Neoguitarist/captobox/resources/CAO carte électronique/fichiers sources/silk/capto.png

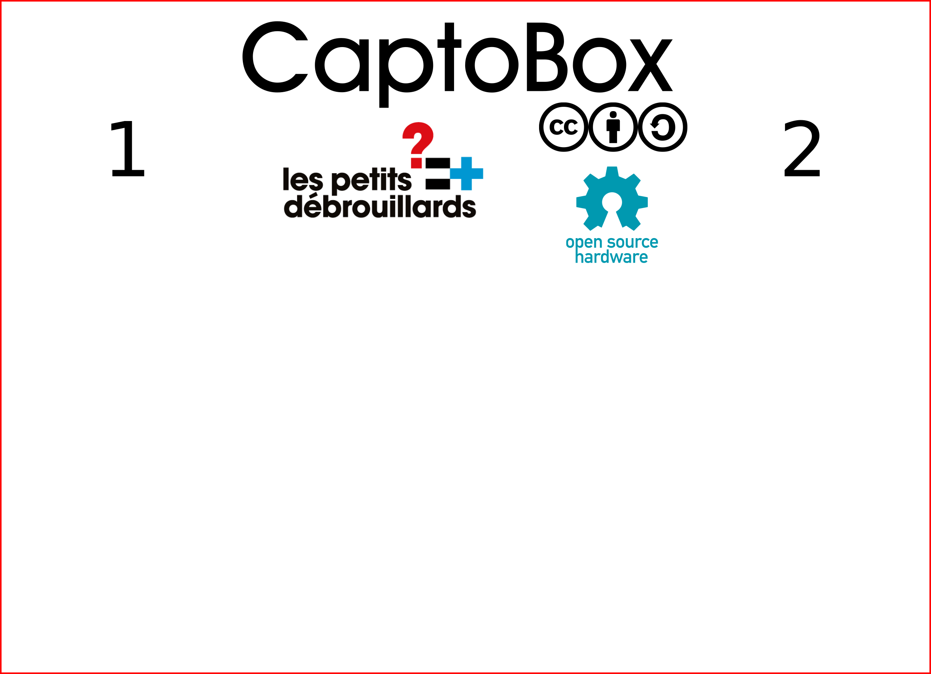
resources/CAO carte électronique/fichiers sources/silk/capto.png
