Neoguitarist/captobox/resources/CAO carte électronique/fichiers sources/silk/captobox-B_SilkS.png

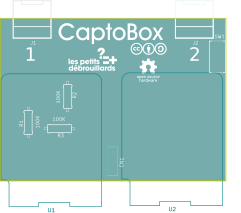
resources/CAO carte électronique/fichiers sources/silk/captobox-B_SilkS.png
