Neoguitarist/captobox/resources/CAO carte électronique/fichiers sources/silk/captobox-F_SilkS.png

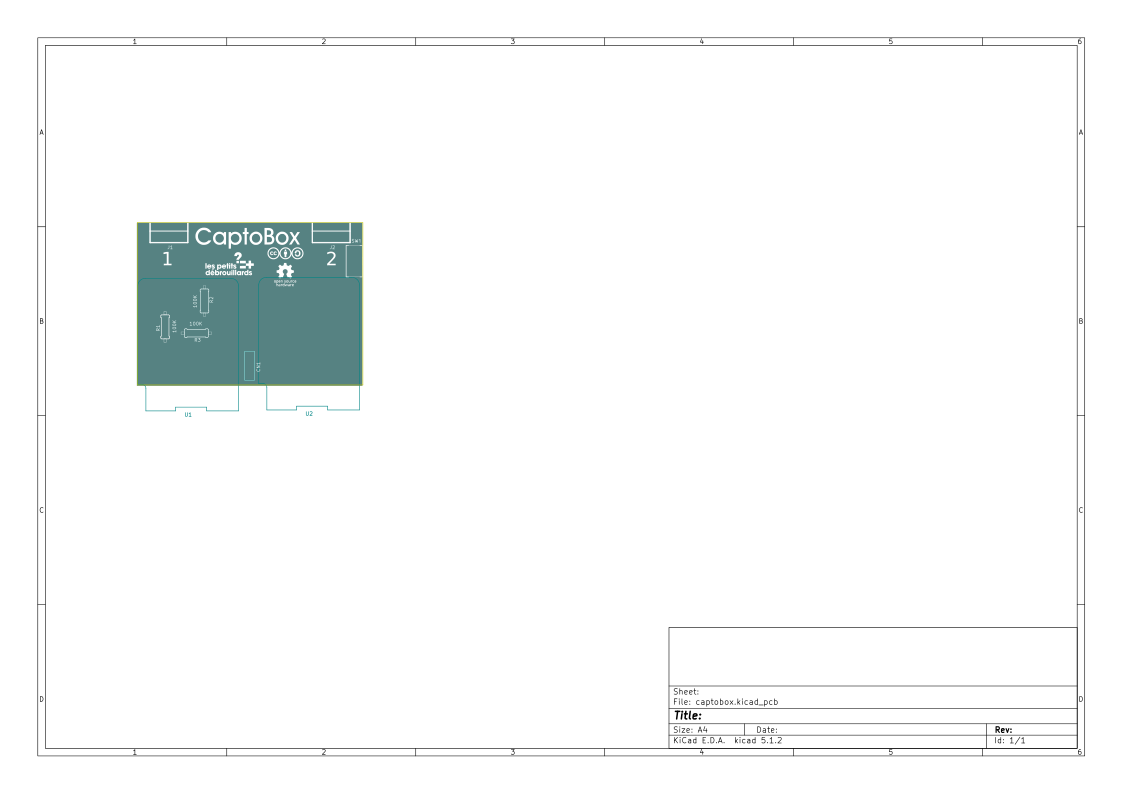
resources/CAO carte électronique/fichiers sources/silk/captobox-F_SilkS.png
