Neoguitarist/captobox/resources/CAO carte électronique/fichiers sources/silk/captobox-final.png

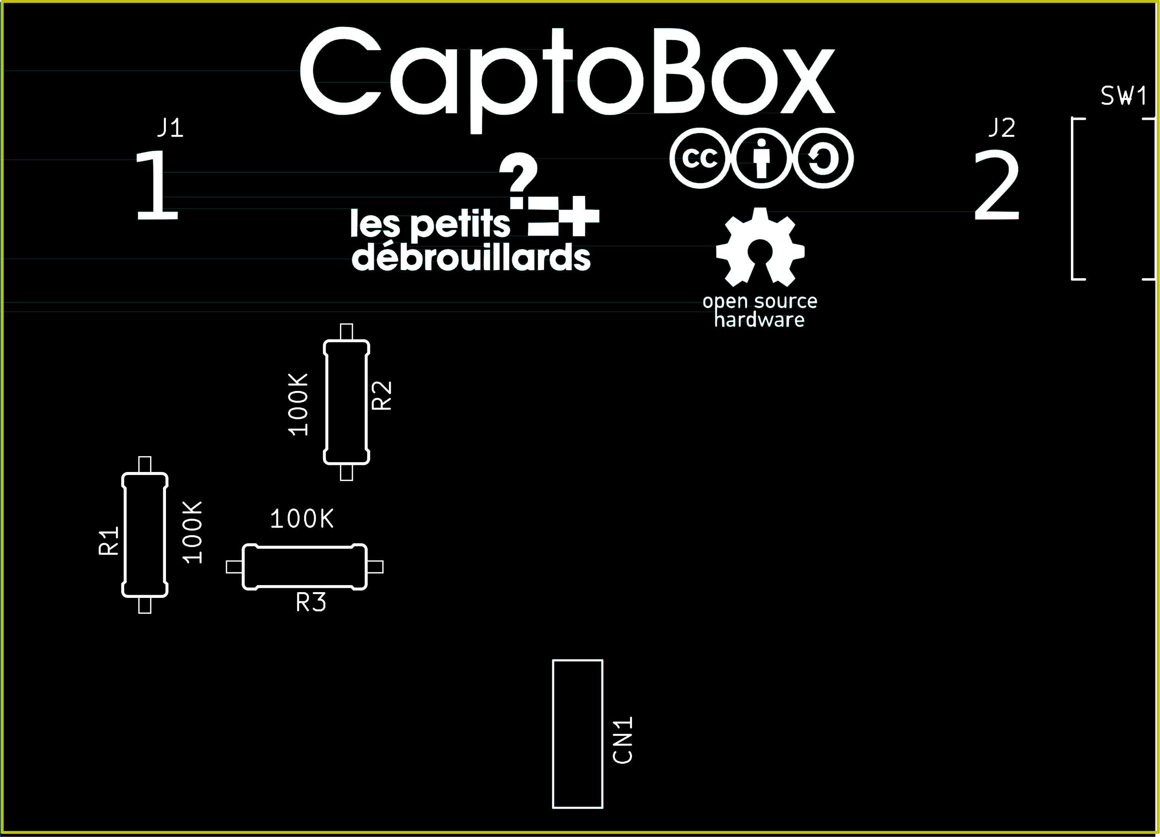
resources/CAO carte électronique/fichiers sources/silk/captobox-final.png
