Neoguitarist/captobox/resources/CAO boitier/wemos_battery.dxf

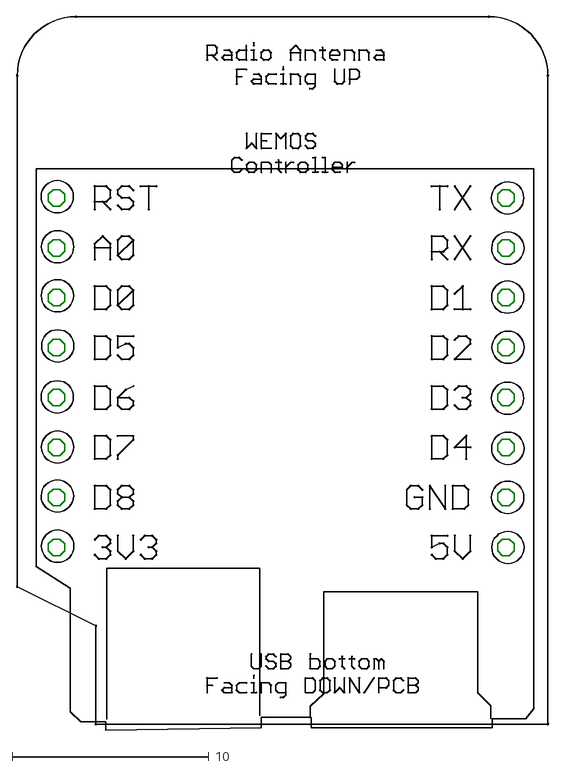
[picture p33: CAD file, 2020-03-02]
resources/CAO boitier/wemos_battery.dxf
27.1 x 36.3
